SpectraCoder/ESP32_Novy_Commander/favicon.h

const static byte FAVICON [] PROGMEM = {
0x89, 0x50, 0x4E, 0x47, 0x0D, 0x0A, 0x1A, 0x0A, 0x00, 0x00, 0x00, 0x0D, 0x49, 0x48, 0x44, 0x52, 
0x00, 0x00, 0x00, 0x28, 0x00, 0x00, 0x00, 0x28, 0x08, 0x06, 0x00, 0x00, 0x00, 0x8C, 0xFE, 0xB8, 
0x6D, 0x00, 0x00, 0x09, 0x39, 0x49, 0x44, 0x41, 0x54, 0x78, 0x9C, 0xEC, 0x58, 0x59, 0x70, 0x93, 
0xD7, 0x15, 0x3E, 0xD2, 0x2F, 0xE9, 0xD7, 0x6E, 0xC9, 0x92, 0x2D, 0x19, 0xCB, 0x96, 0xC0, 0xBB, 
0x59, 0xBC, 0x40, 0x88, 0x49, 0xC0, 0x1B, 0x84, 0x25, 0x29, 0x8B, 0x0D, 0x94, 0xA4, 0x10, 0x63, 
0x96, 0xD2, 0x21, 0x4B, 0x93, 0x69, 0xA7, 0x5B, 0x4A, 0xA7, 0x9D, 0xB6, 0xD3, 0x87, 0x3E, 0xA4, 
0x49, 0xA1, 0x64, 0xA6, 0x2C, 0x26, 0x34, 0x2D, 0x21, 0x4E, 0x30, 0x6E, 0x59, 0x1C, 0x86, 0x80, 
0x8D, 0xDD, 0xC1, 0x06, 0x6F, 0xC2, 0xB5, 0x2C, 0x6C, 0x19, 0x6F, 0xB2, 0xB1, 0x2C, 0x59, 0x96, 
0x25, 0xD9, 0x96, 0x64, 0xC9, 0xEE, 0x9C, 0xEB, 0x48, 0x13, 0x40, 0x60, 0x25, 0x7E, 0xE1, 0x81, 
0x33, 0x73, 0xC7, 0x97, 0x73, 0xBF, 0xFB, 0x9D, 0x8F, 0xBB, 0x9C, 0x73, 0x7F, 0x31, 0xE1, 0x29, 
0xB7, 0x67, 0x02, 0xE7, 0x6A, 0xCF, 0x04, 0xCE, 0xD5, 0xA8, 0x50, 0x40, 0x8A, 0xC8, 0x70, 0x90, 
0x88, 0x85, 0xC0, 0xA5, 0x39, 0x30, 0x3E, 0xE1, 0x7A, 0x64, 0x5C, 0x1E, 0x2E, 0x81, 0xE4, 0xA4, 
0x04, 0x60, 0xB3, 0xA8, 0xDF, 0x84, 0x89, 0x45, 0x39, 0x71, 0x0B, 0xE6, 0xDF, 0x98, 0xF4, 0x78, 
0x82, 0x62, 0x23, 0x64, 0x12, 0x90, 0x4A, 0x44, 0xC0, 0xE7, 0x73, 0x61, 0x6C, 0x6C, 0x62, 0xEE, 
0x02, 0xA3, 0x14, 0x72, 0x78, 0xFE, 0xB9, 0x4C, 0x80, 0xE9, 0xA9, 0xA3, 0xF1, 0x71, 0x71, 0x17, 
0x9D, 0x4E, 0x07, 0x38, 0xC7, 0x26, 0x40, 0x2C, 0x12, 0x40, 0x94, 0x32, 0x02, 0x24, 0x61, 0x22, 
0x08, 0x97, 0x8A, 0xF1, 0xEF, 0x1F, 0x0F, 0x1C, 0xD8, 0xFB, 0xB3, 0x17, 0x5F, 0xCC, 0x5A, 0x69, 
0xE8, 0x68, 0xE7, 0x53, 0x14, 0xE3, 0x1A, 0x9F, 0xCF, 0x23, 0xE3, 0x53, 0x53, 0x53, 0xE0, 0xF6, 
0x4C, 0x82, 0x32, 0x52, 0x06, 0x4B, 0x33, 0xD2, 0x80, 0x62, 0x32, 0x8E, 0xA6, 0x24, 0x27, 0x5D, 
0xB4, 0xDB, 0xED, 0xE0, 0x1C, 0x1B, 0x7F, 0x62, 0xFC, 0x59, 0xB7, 0x58, 0x24, 0xE4, 0x83, 0xD5, 
0x6A, 0x3D, 0xFB, 0xE6, 0x9B, 0x07, 0xF7, 0xD8, 0xED, 0xA3, 0x47, 0x84, 0x02, 0x3E, 0x08, 0x05, 
0x3C, 0x58, 0xB2, 0x30, 0x19, 0xE2, 0xE6, 0xAB, 0x0F, 0x4A, 0xC3, 0x44, 0xD7, 0xD9, 0x2C, 0xD6, 
0x75, 0xBB, 0xDD, 0xFE, 0x56, 0x5A, 0xDA, 0x12, 0x3E, 0x36, 0xEC, 0xA3, 0x0F, 0xC7, 0x10, 0x83, 
0x58, 0x9C, 0x83, 0x73, 0x91, 0x03, 0xB9, 0x90, 0x13, 0xB9, 0x67, 0x33, 0xD6, 0xAC, 0x08, 0x00, 
0x70, 0x3A, 0x9D, 0x2B, 0xE2, 0xE2, 0xE3, 0xB8, 0x3E, 0x9F, 0x37, 0x73, 0xBE, 0x46, 0x0D, 0x32, 
0x59, 0x38, 0x48, 0xA5, 0x92, 0x1D, 0xE9, 0xE9, 0x69, 0x87, 0x96, 0x3D, 0xB7, 0x74, 0x1E, 0x62, 
0x8E, 0x1F, 0x3B, 0x19, 0xC0, 0xAB, 0x54, 0xAA, 0xB0, 0xFD, 0x3F, 0xDC, 0x9B, 0x8B, 0xFD, 0xFA, 
0xDB, 0x0D, 0x89, 0xCD, 0xCD, 0x5A, 0xEB, 0xC2, 0x94, 0xC4, 0xB3, 0x62, 0x91, 0x08, 0x1C, 0x8E, 
0xD1, 0x4C, 0xE4, 0x42, 0xCE, 0x50, 0x62, 0x33, 0x66, 0x03, 0x24, 0xC6, 0xC5, 0xC2, 0xC2, 0xD4, 
0xE4, 0x28, 0x00, 0xC6, 0x40, 0xE1, 0xD6, 0x2D, 0xEE, 0x0F, 0x3F, 0x38, 0x5C, 0x3E, 0x3D, 0x3D, 
0x7D, 0x3A, 0x3F, 0x3F, 0xEF, 0x13, 0x9A, 0xA6, 0x25, 0x37, 0x6F, 0xD6, 0x12, 0xDC, 0xBE, 0xFD, 
0x7B, 0xA1, 0xF4, 0xB3, 0xCF, 0x49, 0x7F, 0xFB, 0xF7, 0xB7, 0xC1, 0x89, 0xE3, 0x33, 0x82, 0x57, 
0xAC, 0xC8, 0x02, 0xB7, 0xDB, 0x6D, 0xBB, 0x76, 0xED, 0xFA, 0x2E, 0x06, 0x83, 0x51, 0xF4, 0xCE, 
0xBB, 0x6F, 0x6F, 0x3E, 0xF7, 0xC5, 0x79, 0x1A, 0x60, 0x7A, 0x5E, 0xAB, 0x4E, 0x7F, 0xBF, 0xBD, 
0xB3, 0xF7, 0x89, 0xF1, 0x67, 0x5D, 0x41, 0x24, 0x60, 0xB3, 0x59, 0xF7, 0x95, 0x0A, 0x05, 0x88, 
0xC5, 0x62, 0xDA, 0xE7, 0xF3, 0x45, 0x32, 0x99, 0x4C, 0x3E, 0x9B, 0xCD, 0x96, 0xE0, 0xD9, 0xB2, 
0x5A, 0xAD, 0x04, 0x27, 0x20, 0xDB, 0x67, 0x0F, 0xF4, 0xFD, 0x7E, 0xC4, 0x20, 0x16, 0x00, 0xF8, 
0x38, 0x17, 0x39, 0x10, 0x37, 0x68, 0x32, 0xCD, 0x2A, 0x2E, 0x24, 0x81, 0x7E, 0xE3, 0x70, 0x38, 
0x0D, 0x66, 0xB3, 0x65, 0xA9, 0x46, 0xA3, 0x16, 0x3B, 0x1C, 0xCE, 0x70, 0x97, 0xCB, 0xD5, 0x2D, 
0x14, 0x0A, 0x35, 0xF1, 0xF1, 0xF1, 0x64, 0xDC, 0x6C, 0xB6, 0x80, 0xD7, 0xEB, 0x0D, 0xF4, 0xFD, 
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
};
